boda-akos/CH32V003-Matchbox-Binary-Clock/20251216_145756.jpg

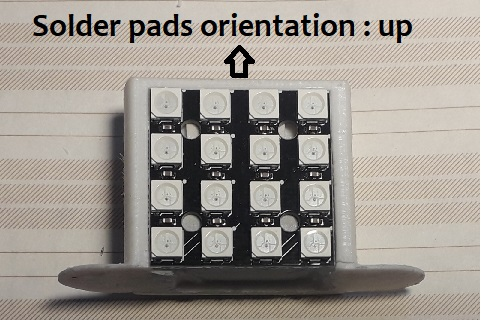
20251216_145756.jpg
