boda-akos/CH32V003-Matchbox-Binary-Clock/20251216_145820.jpg

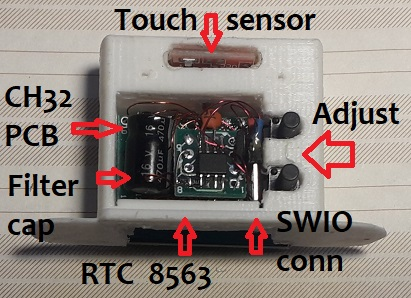
20251216_145820.jpg
