boda-akos/CH32V003-Matchbox-Binary-Clock/20251217_090210.jpg

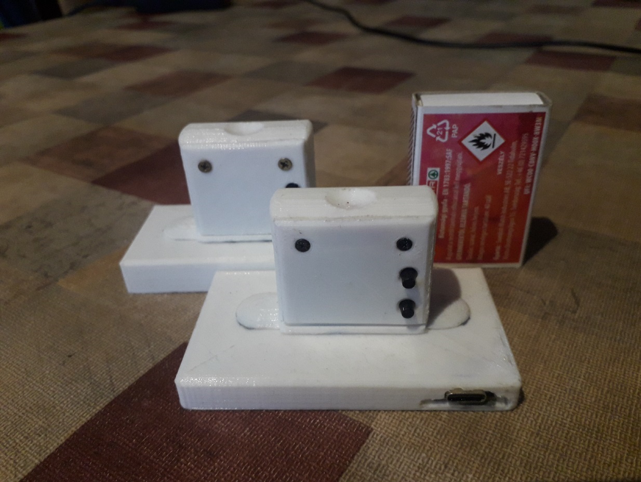
20251217_090210.jpg
